ooguzhanesen/HidroNode_Hardware_Project/docs/Images/WhatsApp Image 2025-12-24 at 20.03.53.jpeg

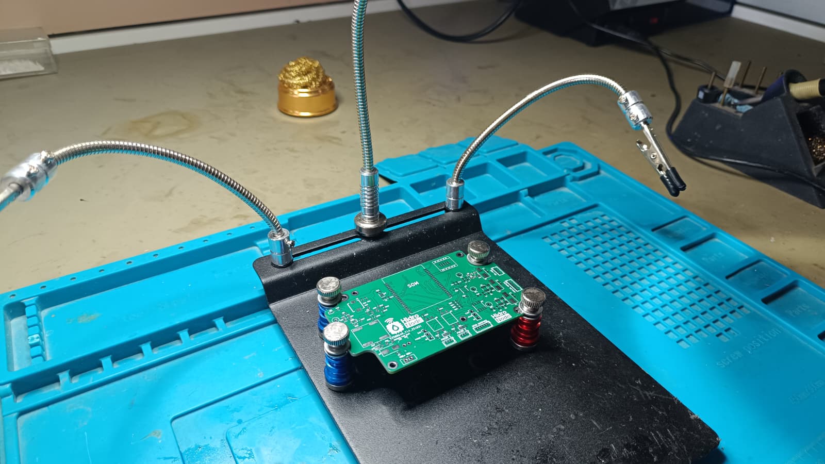
docs/Images/WhatsApp Image 2025-12-24 at 20.03.53.jpeg
